pieeg-club/EEGwithRaspberryPI/Supplementary files/Fig.1..jpg

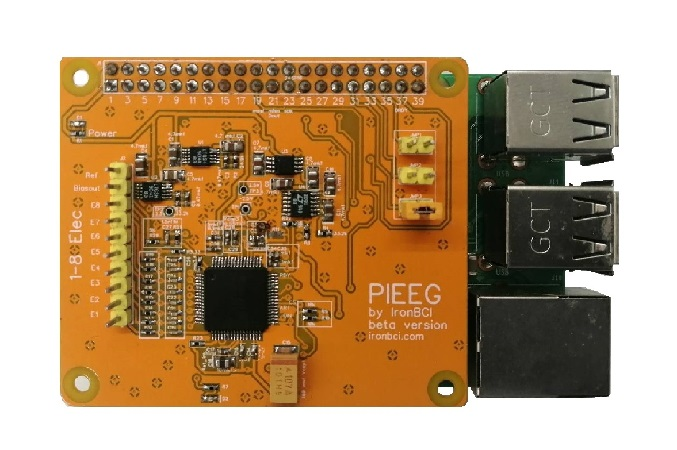
Supplementary files/Fig.1..jpg
