pieeg-club/EEGwithRaspberryPI/Supplementary files/Fig.2.jpg.jpg

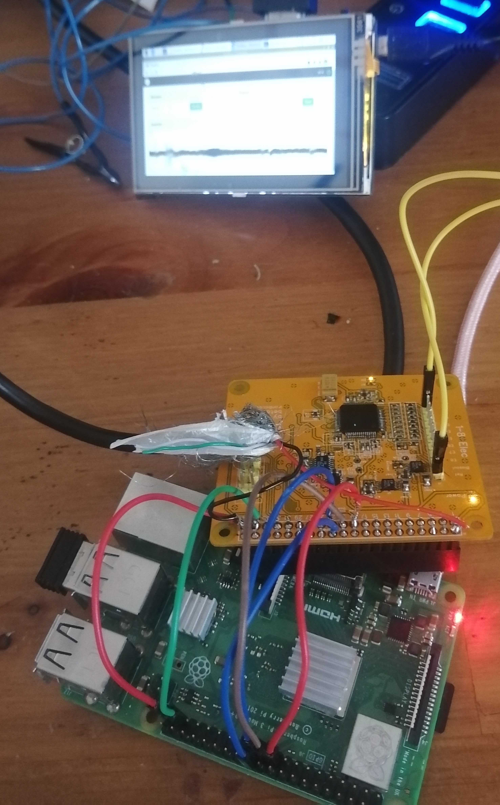
Supplementary files/Fig.2.jpg.jpg
