pieeg-club/EEGwithRaspberryPI/Supplementary files/Fig.4.jpg

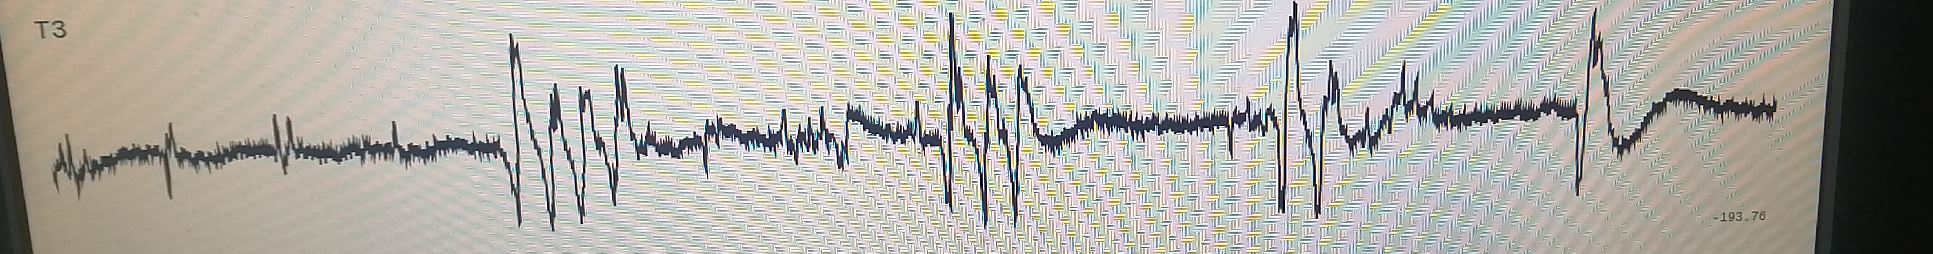
Supplementary files/Fig.4.jpg
