pieeg-club/EEGwithRaspberryPI/Supplementary files/Fig.5.jpg

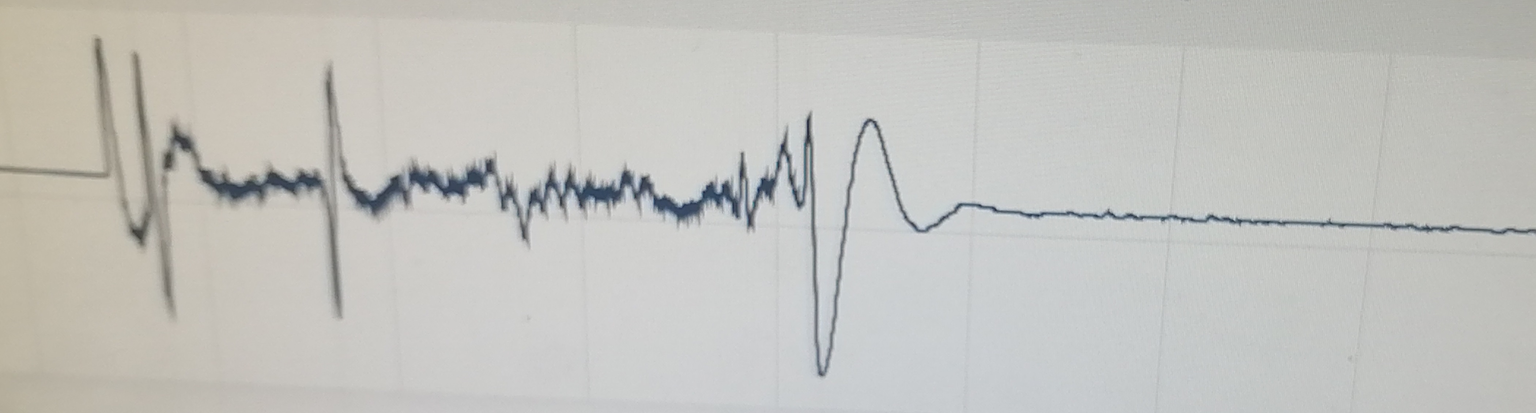
Supplementary files/Fig.5.jpg
