pieeg-club/EEGwithRaspberryPI/Supplementary files/Fig.6.jpg

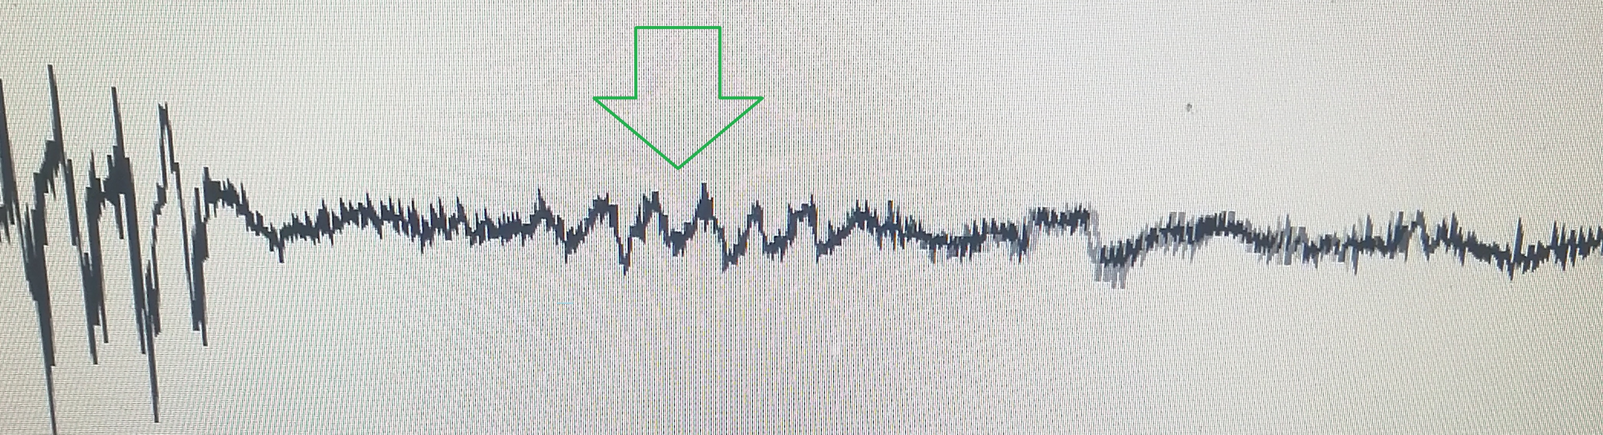
Supplementary files/Fig.6.jpg
