pieeg-club/EEGwithRaspberryPI/Supplementary files/Fig.8..jpg

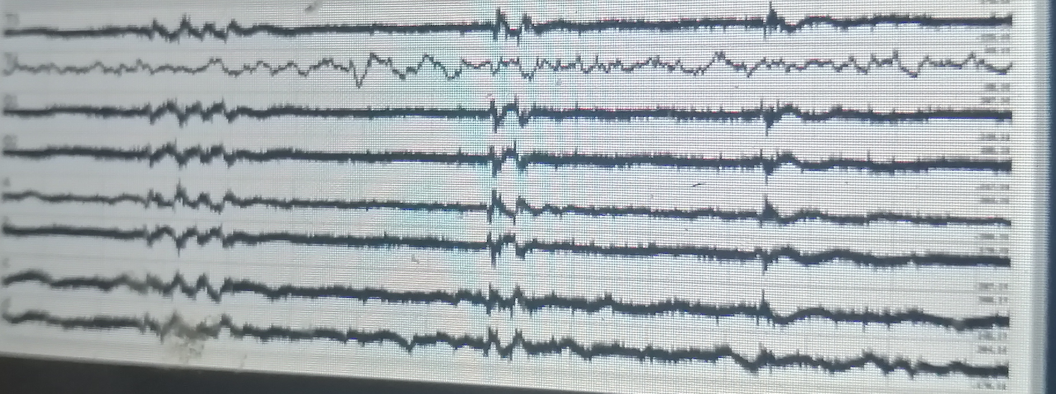
Supplementary files/Fig.8..jpg
