pieeg-club/EEGwithRaspberryPI/Supplementary files/Fig.11.alpha.bmp

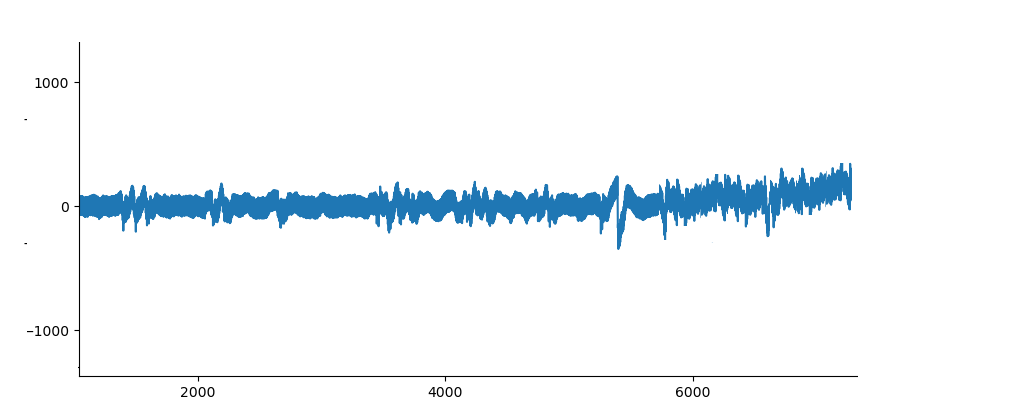
Supplementary files/Fig.11.alpha.bmp
