pieeg-club/EEGwithRaspberryPI/Supplementary files/fig.12.bmp

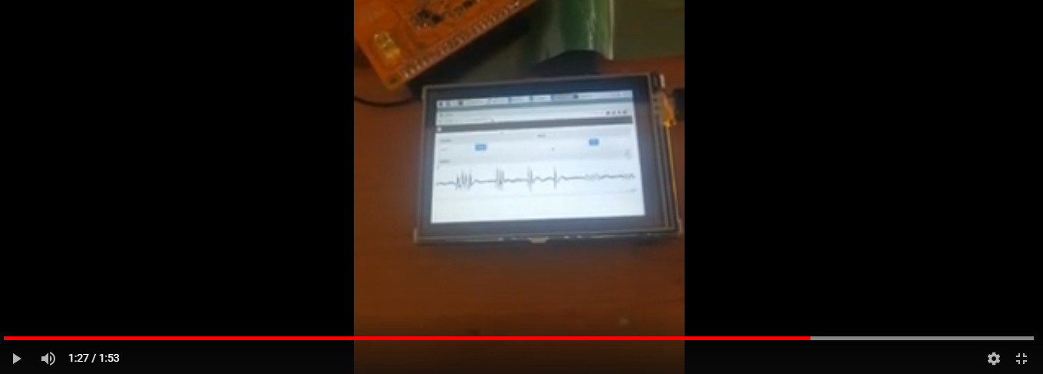
Supplementary files/fig.12.bmp
