pieeg-club/EEGwithRaspberryPI/Supplementary files/fig.14.jpg

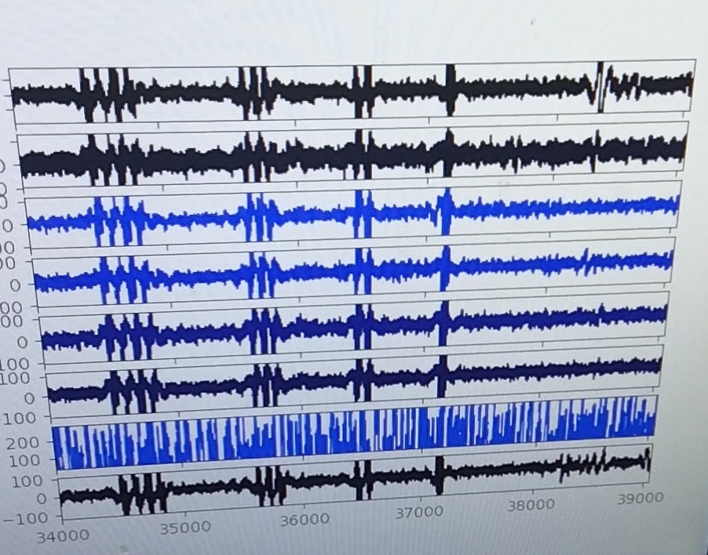
Supplementary files/fig.14.jpg
