pieeg-club/EEGwithRaspberryPI/Supplementary files/fig.15...jpg

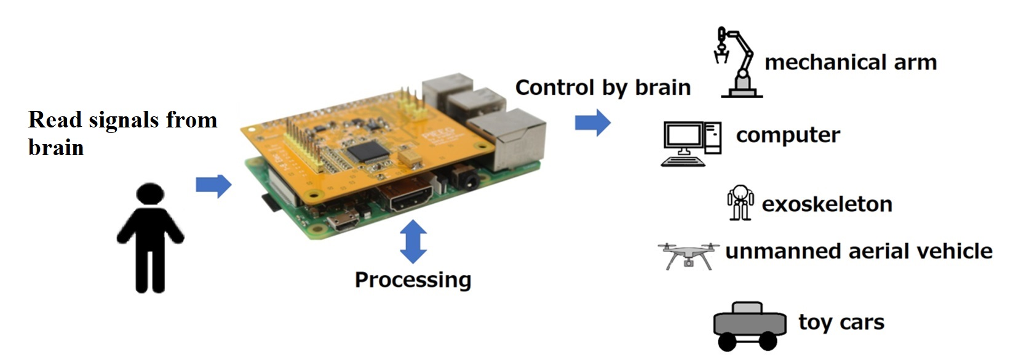
Supplementary files/fig.15...jpg
