pieeg-club/EEGwithRaspberryPI/Supplementary files/noise/img1.jpg

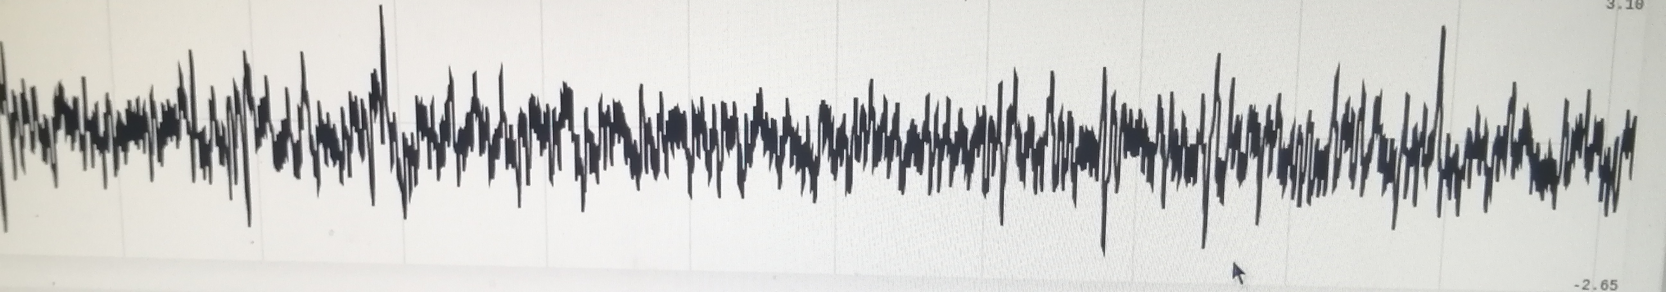
Supplementary files/noise/img1.jpg
