pieeg-club/EEGwithRaspberryPI/Supplementary files/noise/img_2.jpg

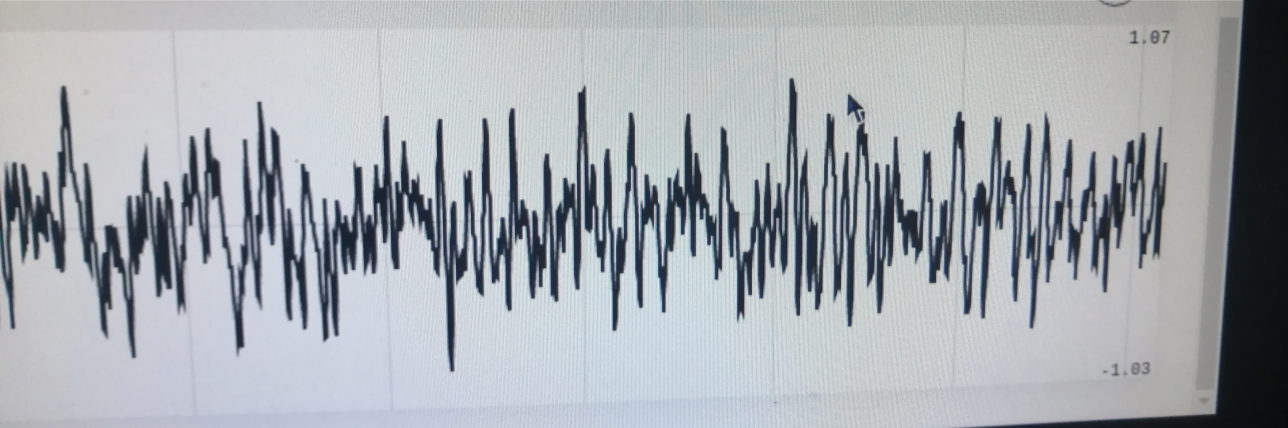
Supplementary files/noise/img_2.jpg
