pieeg-club/EEGwithRaspberryPI/Supplementary files/works1.bmp

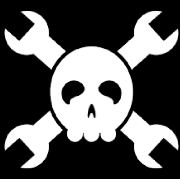
Supplementary files/works1.bmp
